zhelezyaka/rc-ppm-2-spi/pcb/ppm2spi.sch

## KiCad design pcb/ppm2spi.sch (2013-11-08)

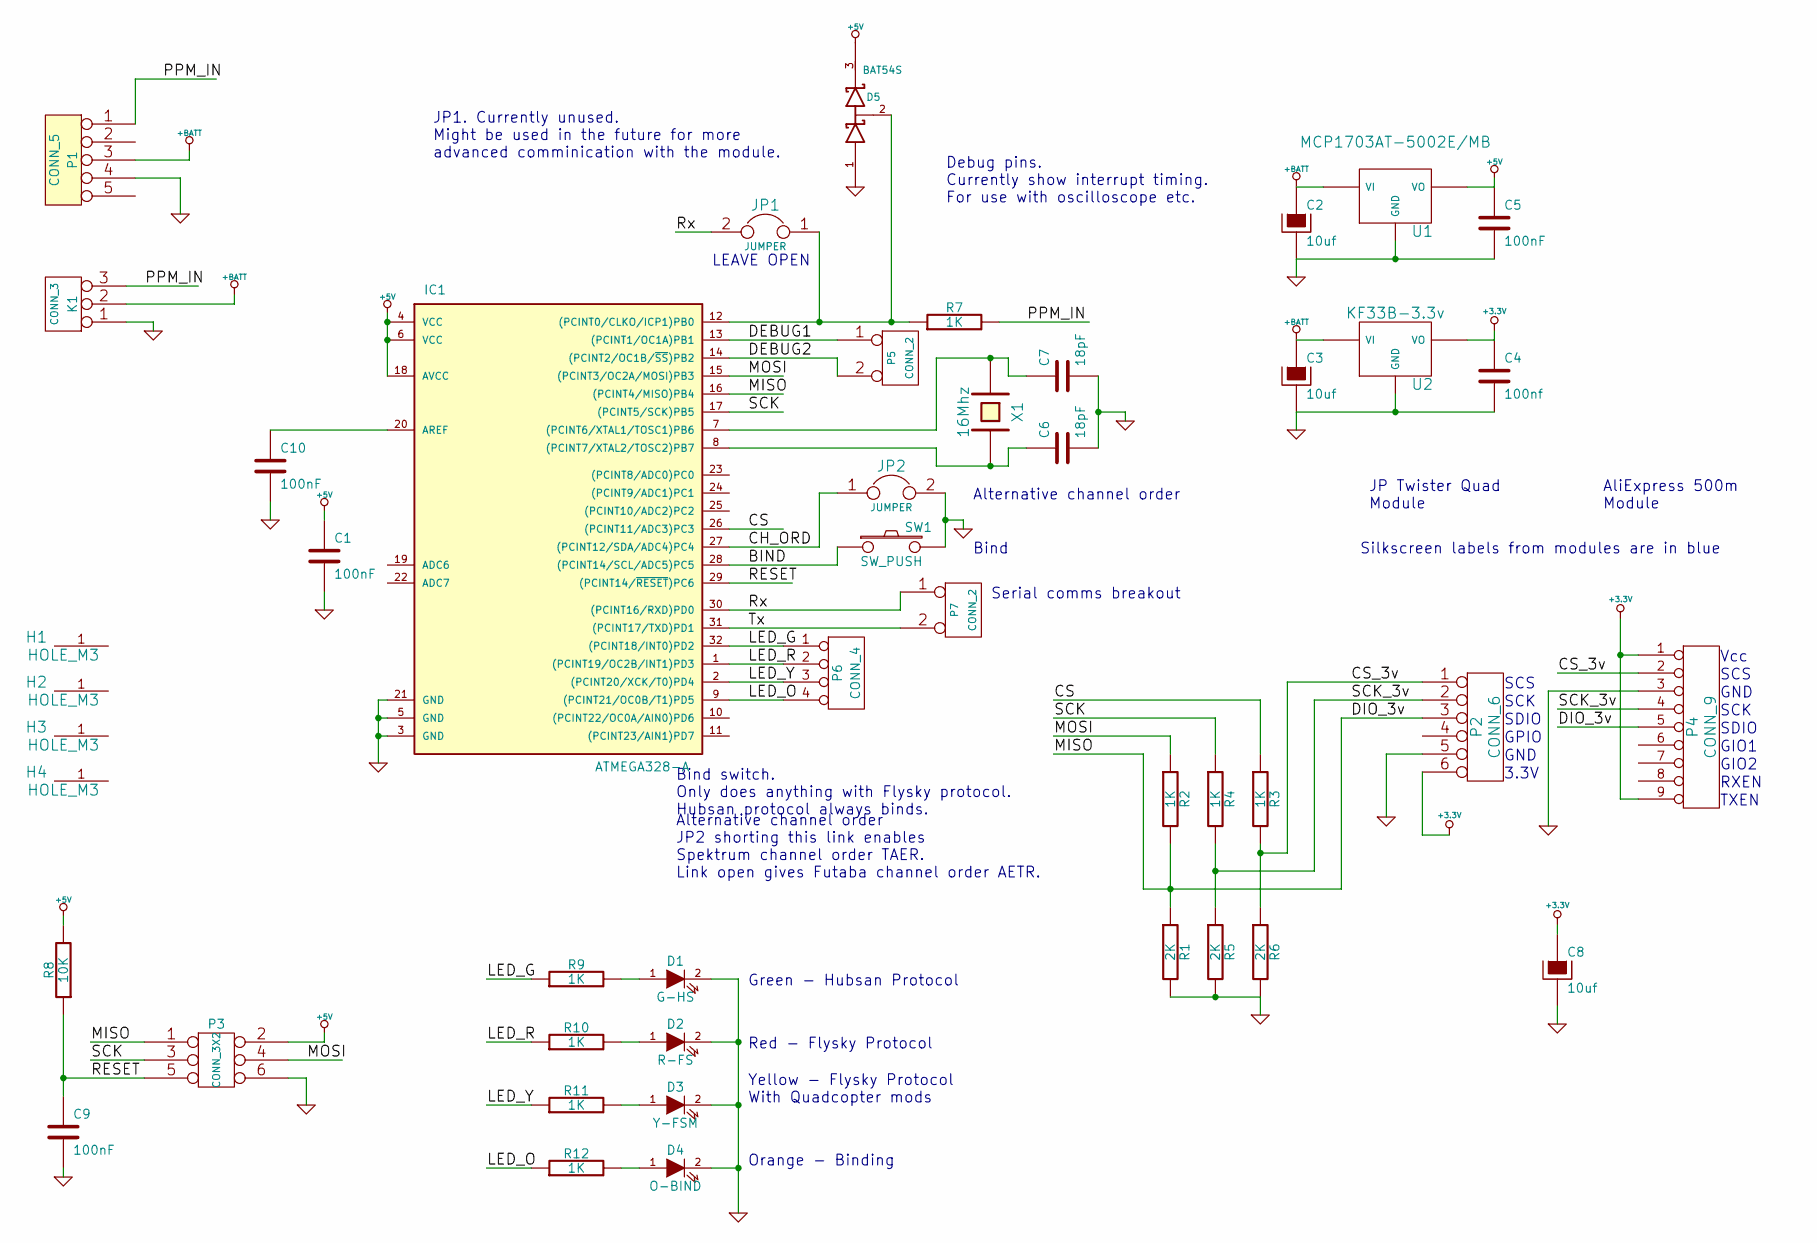
[picture p8: schematic ppm2spi.sch]

Parts:
C1, C5, C9, C10: 100nF
C2, C3, C8: 10uf
C4: 100nf
C6, C7: 18pF
D1: G-HS
D2: R-FS
D3: Y-FSM
D4: O-BIND
D5: BAT54S
H1, H2, H3, H4: HOLE_M3
IC1: ATMEGA328-A; TQFP32
JP1, JP2: JUMPER
K1: CONN_3
P1: CONN_5
P2: CONN_6
P3: CONN_3X2
P4: CONN_9
P5, P7: CONN_2
P6: CONN_4
R1, R5, R6: 2K
R2, R3, R4, R7, R9, R10, R11, R12: 1K
R8: 10K
SW1: SW_PUSH
U1: MCP1703AT-5002E/MB
U2: KF33B-3.3v
X1: 16Mhz

Connections:
+3.3V: C4.1, C8.1, P2.6, P4.1, P4.9, U2.VO
+5V: C1.1, C5.1, D5.3 (cathode), IC1.4 (VCC), IC1.6 (VCC), IC1.18 (AVCC), P3.2, R8.2, U1.VO
+BATT: C2.1, C3.1, K1.2 (PM), P1.3, U1.VI, U2.VI
BIND: IC1.28 ((PCINT14/SCL/ADC5)PC5), SW1.1
CH_ORD: IC1.27 ((PCINT12/SDA/ADC4)PC4), JP2.1
CS: IC1.26 ((PCINT11/ADC3)PC3), R3.1
CS_3v: P2.1, P4.2, R3.2, R6.1
DEBUG1: IC1.13 ((PCINT1/OC1A)PB1), P5.1
DEBUG2: IC1.14 ((PCINT2/OC1B/~SS~)PB2), P5.2 (PM)
DIO_3v: IC1.16 ((PCINT4/MISO)PB4), P2.3, P3.1, P4.5, R1.1, R2.2
GND: C1.2, C2.2, C3.2, C4.2, C5.2, C6.2, C7.2, C8.2, C9.2, C10.2, D1.2 (K), D2.2 (K), D3.2 (K), D4.2 (K), D5.1 (Anode), IC1.3 (GND), IC1.5 (GND), IC1.21 (GND), JP2.2, K1.1, P1.4, P2.5, P3.6, P4.3, R1.2, R5.2, R6.2, SW1.2, U1.GND, U2.GND
LED_G: IC1.32 ((PCINT18/INT0)PD2), P6.1, R9.1
LED_O: IC1.9 ((PCINT21/OC0B/T1)PD5), P6.4, R12.1
LED_R: IC1.1 ((PCINT19/OC2B/INT1)PD3), P6.2, R10.1
LED_Y: IC1.2 ((PCINT20/XCK/T0)PD4), P6.3, R11.1
MOSI: IC1.15 ((PCINT3/OC2A/MOSI)PB3), P3.4, R2.1
unnamed: C6.1, IC1.8 ((PCINT7/XTAL2/TOSC2)PB7), X1.2
unnamed: C7.1, IC1.7 ((PCINT6/XTAL1/TOSC1)PB6), X1.1
unnamed: C10.1, IC1.20 (AREF)
unnamed: D1.1 (A), R9.2
unnamed: D2.1 (A), R10.2
unnamed: D3.1 (A), R11.2
unnamed: D4.1 (A), R12.2
unnamed: D5.2 (AK), IC1.12 ((PCINT0/CLKO/ICP1)PB0), JP1.1, R7.1
PPM_IN: K1.3, P1.1, R7.2
RESET: C9.1, IC1.29 ((PCINT14/~RESET~)PC6), P3.5, R8.1
Rx: IC1.30 ((PCINT16/RXD)PD0), JP1.2, P7.1
SCK: IC1.17 ((PCINT5/SCK)PB5), P3.3, R4.1
SCK_3v: P2.2, P4.4, R4.2, R5.1
Tx: IC1.31 ((PCINT17/TXD)PD1), P7.2 (PM)

Notes on the sheet:
AliExpress 500m Module
JP Twister Quad Module
SCS
SCK
SDIO
GPIO
GND
3.3V
Vcc
GIO1
GIO2
RXEN
TXEN
Silkscreen labels from modules are in blue
Bind switch. Only does anything with Flysky protocol. Hubsan protocol always binds.
Debug pins. Currently show interrupt timing. For use with oscilloscope etc.
LEAVE OPEN
JP1. Currently unused. Might be used in the future for more advanced comminication with the module.
Green - Hubsan Protocol
Yellow - Flysky Protocol With Quadcopter mods
Red - Flysky Protocol
Orange - Binding
Bind
Alternative channel order
Alternative channel order JP2 shorting this link enables Spektrum channel order TAER. Link open gives Futaba channel order AETR.
Serial comms breakout
