zhelezyaka/rc-ppm-2-spi/code/hubsan_a7105.c

/*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
 This file is based on work by PhracturedBlue (real name and email ?)
 It can be found here:
 https://bitbucket.org/PhracturedBlue/deviation/src
 
 Alterations by Cameron Weeks <th9xer@gmail.com>
 http://code.google.com/p/rc-ppm-2-spi/
 */

#ifdef MODULAR
  //Allows the linker to properly relocate
  #define HUBSAN_Cmds PROTO_Cmds
  #pragma long_calls
#endif

#include "common.h"
#include "iface_a7105.h"     // Edit by cam - Added
#include "misc.h"            // Edit by cam - Added
//#include "interface.h"     // Edit by cam - Commented out
//#include "mixer.h"         // Edit by cam - Commented out
//#include "config/model.h"  // Edit by cam - Commented out
#include <string.h>
#include <stdlib.h>


#ifdef MODULAR
  //Some versions of gcc applythis to definitions, others to calls
  //So just use long_calls everywhere
  //#pragma long_calls_off
  extern unsigned _data_loadaddr;
  const unsigned long protocol_type = (unsigned long)&_data_loadaddr;
#endif
#ifdef PROTO_HAS_A7105

enum{
    FLAG_FLIP = 0x08,
    FLAG_LED  = 0x04
};

static u8 packet[16];
static u8 channel;
static const u8 allowed_ch[] = {0x14, 0x1e, 0x28, 0x32, 0x3c, 0x46, 0x50, 0x5a, 0x64, 0x6e, 0x78, 0x82};
static u32 sessionid;
static const u32 txid = 0xdb042679;
static u8 state;
static u8 packet_count;
enum {
    BIND_1,
    BIND_2,
    BIND_3,
    BIND_4,
    BIND_5,
    BIND_6,
    BIND_7,
    BIND_8,
    DATA_1,
    DATA_2,
    DATA_3,
    DATA_4,
    DATA_5,
};
#define WAIT_WRITE 0x80

static void hubsan_init()
{
    u8 if_calibration1;
    u8 vco_calibration0;
    u8 vco_calibration1;
    //u8 vco_current;

    A7105_WriteID(0x55201041);
    A7105_WriteReg(A7105_01_MODE_CONTROL, 0x63);
    A7105_WriteReg(A7105_03_FIFOI, 0x0f);
    A7105_WriteReg(A7105_0D_CLOCK, 0x05);
    A7105_WriteReg(A7105_0E_DATA_RATE, 0x04);
    A7105_WriteReg(A7105_15_TX_II, 0x2b);
    A7105_WriteReg(A7105_18_RX, 0x62);
    A7105_WriteReg(A7105_19_RX_GAIN_I, 0x80);
    A7105_WriteReg(A7105_1C_RX_GAIN_IV, 0x0A);
    A7105_WriteReg(A7105_1F_CODE_I, 0x07);
    A7105_WriteReg(A7105_20_CODE_II, 0x17);
    A7105_WriteReg(A7105_29_RX_DEM_TEST_I, 0x47);

    A7105_Strobe(A7105_STANDBY);

    //IF Filter Bank Calibration
    A7105_WriteReg(0x02, 1);
    //vco_current =
    A7105_ReadReg(0x02);
    while(A7105_ReadReg(0x02))
        ;
    if_calibration1 = A7105_ReadReg(A7105_22_IF_CALIB_I);
    A7105_ReadReg(A7105_24_VCO_CURCAL);
    if(if_calibration1 & A7105_MASK_FBCF) {
        //Calibration failed...what do we do?
    }

    //VCO Current Calibration
    //A7105_WriteReg(0x24, 0x13); //Recomended calibration from A7105 Datasheet

    //VCO Bank Calibration
    //A7105_WriteReg(0x26, 0x3b); //Recomended limits from A7105 Datasheet

    //VCO Bank Calibrate channel 0?
    //Set Channel
    A7105_WriteReg(A7105_0F_CHANNEL, 0);
    //VCO Calibration
    A7105_WriteReg(0x02, 2);
    while(A7105_ReadReg(0x02))
        ;
    vco_calibration0 = A7105_ReadReg(A7105_25_VCO_SBCAL_I);
    if (vco_calibration0 & A7105_MASK_VBCF) {
        //Calibration failed...what do we do?
    }

    //Calibrate channel 0xa0?
    //Set Channel
    A7105_WriteReg(A7105_0F_CHANNEL, 0xa0);
    //VCO Calibration
    A7105_WriteReg(A7105_02_CALC, 2);
    while(A7105_ReadReg(A7105_02_CALC))
        ;
    vco_calibration1 = A7105_ReadReg(A7105_25_VCO_SBCAL_I);
    if (vco_calibration1 & A7105_MASK_VBCF) {
        //Calibration failed...what do we do?
    }

    //Reset VCO Band calibration
    //A7105_WriteReg(0x25, 0x08);

    A7105_SetPower(Model.tx_power);

    A7105_Strobe(A7105_STANDBY);
}

static void update_crc()
{
    int sum = 0;
    for(int i = 0; i < 15; i++)
        sum += packet[i];
    packet[15] = (256 - (sum % 256)) & 0xff;
}
static void hubsan_build_bind_packet(u8 state)
{
    packet[0] = state;
    packet[1] = channel;
    packet[2] = (sessionid >> 24) & 0xff;
    packet[3] = (sessionid >> 16) & 0xff;
    packet[4] = (sessionid >>  8) & 0xff;
    packet[5] = (sessionid >>  0) & 0xff;
    packet[6] = 0x08;
    packet[7] = 0xe4; //???
    packet[8] = 0xea;
    packet[9] = 0x9e;
    packet[10] = 0x50;
    packet[11] = (txid >> 24) & 0xff;
    packet[12] = (txid >> 16) & 0xff;
    packet[13] = (txid >>  8) & 0xff;
    packet[14] = (txid >>  0) & 0xff;
    update_crc();
}

static s16 get_channel(u8 ch, s32 scale, s32 center, s32 range)
{
    s32 value = (s32)Channels[ch] * scale / CHAN_MAX_VALUE + center;
    if (value < center - range)
        value = center - range;
    if (value >= center + range)
        value = center + range -1;
    return value;
}

static void hubsan_build_packet()
{
    memset(packet, 0, 16);
    //20 00 00 00 80 00 7d 00 84 02 64 db 04 26 79 7b
    packet[0] = 0x20;
    packet[2] = get_channel(2, 0x80, 0x80, 0x80);
    packet[4] = 0xff - get_channel(3, 0x80, 0x80, 0x80); //Rudder is reversed
    packet[6] = 0xff - get_channel(1, 0x80, 0x80, 0x80); //Elevator is reversed
    packet[8] = get_channel(0, 0x80, 0x80, 0x80);
    if(packet_count < 100)
    {
        packet[9] = 0x02 | FLAG_LED | FLAG_FLIP; // sends default value for the 100 first packets
        packet_count++;
    }
    else
    {
	    // On threshold set as 400 = 1500us + 20us, so 20us above centre
        packet[9] = 0x02;
        if(Channels[4] >= 400)
            packet[9] |= FLAG_LED;
        if(Channels[5] >= 400)
            packet[9] |= FLAG_FLIP;
    }
    packet[10] = 0x64;
    packet[11] = (txid >> 24) & 0xff;
    packet[12] = (txid >> 16) & 0xff;
    packet[13] = (txid >>  8) & 0xff;
    packet[14] = (txid >>  0) & 0xff;
    update_crc();
}

//MODULE_CALLTYPE   //Edit by cam - Commented out
static u16 hubsan_cb()
{
    int i;
    switch(state) {
    case BIND_1:
    case BIND_3:
    case BIND_5:
    case BIND_7:
        hubsan_build_bind_packet(state == BIND_7 ? 9 : (state == BIND_5 ? 1 : state + 1 - BIND_1));
        A7105_Strobe(A7105_STANDBY);
        A7105_WriteData(packet, 16, channel);
        state |= WAIT_WRITE;
        return 3000;
    case BIND_1 | WAIT_WRITE:
    case BIND_3 | WAIT_WRITE:
    case BIND_5 | WAIT_WRITE:
    case BIND_7 | WAIT_WRITE:
        //wait for completion
        for(i = 0; i< 20; i++) {
           if(! (A7105_ReadReg(A7105_00_MODE) & 0x01))
               break;
        }
        //if (i == 20)
        //    printf("Failed to complete write\n");
        A7105_Strobe(A7105_RX);
        state &= ~WAIT_WRITE;
        state++;
        return 4500; //7.5msec elapsed since last write
    case BIND_2:
    case BIND_4:
    case BIND_6:
        if(A7105_ReadReg(A7105_00_MODE) & 0x01) {
            state = BIND_1;
            return 4500; //No signal, restart binding procedure.  12msec elapsed since last write
        }
        A7105_ReadData(packet, 16);
        state++;
        if (state == BIND_5)
		    // Edit by Cam - cast to u32 to stop compiler warning
            A7105_WriteID(((u32)packet[2] << 24) | ((u32)packet[3] << 16) | ((u32)packet[4] << 8) | packet[5]);
        
        return 500;  //8msec elapsed time since last write;
    case BIND_8:
        if(A7105_ReadReg(A7105_00_MODE) & 0x01) {
            state = BIND_7;
            return 15000; //22.5msec elapsed since last write
        }
        A7105_ReadData(packet, 16);
        if(packet[1] == 9) {
            state = DATA_1;
            A7105_WriteReg(A7105_1F_CODE_I, 0x0F);
            PROTOCOL_SetBindState(0);
			g_initializing = 0;   //Edit by cam - added to indicate normal data transmission has begun
            return 28000; //35.5msec elapsed since last write
        } else {
            state = BIND_7;
            return 15000; //22.5 msec elapsed since last write
        }
    case DATA_1:
        //Keep transmit power in sync
        A7105_SetPower(Model.tx_power);
    case DATA_2:
    case DATA_3:
    case DATA_4:
    case DATA_5:
        hubsan_build_packet();
        A7105_WriteData(packet, 16, state == DATA_5 ? channel + 0x23 : channel);
        if (state == DATA_5)
            state = DATA_1;
        else
            state++;
        return 10000;
    }
    return 0;
}

static void initialize() {
    CLOCK_StopTimer();
    A7105_Reset();
    hubsan_init();
	//Edit by Cam - AVR rand() is only 16 bits so double up
    sessionid = rand() + ((u32)rand() << 16);
    channel = allowed_ch[rand() % sizeof(allowed_ch)];
    PROTOCOL_SetBindState(0xFFFFFFFF);
    state = BIND_1;
    packet_count=0;
    CLOCK_StartTimer(10000, hubsan_cb);
}

const void *HUBSAN_Cmds(enum ProtoCmds cmd)
{
    switch(cmd) {
        case PROTOCMD_INIT:  initialize(); return 0;
        case PROTOCMD_DEINIT: return 0;
        case PROTOCMD_CHECK_AUTOBIND: return (void *)1L; //Always autobind
        case PROTOCMD_BIND:  initialize(); return 0;
        case PROTOCMD_NUMCHAN: return (void *)6L;
        case PROTOCMD_DEFAULT_NUMCHAN: return (void *)6L;
        case PROTOCMD_CURRENT_ID: return 0;
        case PROTOCMD_TELEMETRYSTATE: return (void *)(long)-1;
        default: break;
    }
    return 0;
}
#endif
